CAMES-Engineering/EarBolus/ideas/klips til kasse.scad

union(){
cube([40,10,10]);
translate([0,22.3,0])cube([40,10,10]);
translate([0,10,0])cube([10,12.3,10]);
}
