CAMES-Engineering/EarBolus/ideas/w_cprearcylinder.scad

CPRnumber="999999-9999";

import("C:/Users/Sanne/Documents/GitHub/EarBolus/ideas/earcylinder.stl");
color("red")
translate([-27,19,16.3])
linear_extrude(2)
text(CPRnumber,font="Liberation Sans:style=Bold", size=3);
